Karry/hdd-mp3-player/src/command-v2/font-maly.h

////////////////////////////////////////////////////////////////////////
// Malý fotn 6x8. Protože ale LCD má stránky o výšce 8px a byty 
// se do něj zapisují svisle, tak každé pismeno v tomto fontu je na jednom řádku.

unsigned char rom FontMaly[]={ 
	 0x00, 0x00, 0x00, 0x00, 0x00, 0x00, 	// 0x00 - mezera
	 0x00, 0x00, 0xFE, 0x01, 0x01, 0x01, 	// 0x01 - orámování - levý horní
	 0x00, 0x00, 0xFF, 0x00, 0x00, 0x00, 	// 0x02 - orámování - svislý
	 0x01, 0x01, 0xFE, 0x00, 0x00, 0x00, 	// 0x03 - orámování - pravý horní
	 0x00, 0x00, 0x03, 0x04, 0x04, 0x04, 	// 0x04 - orámování - levý dolní
	 0x04, 0x04, 0x03, 0x00, 0x00, 0x00,	// 0x05 - orámování - pravý dolní	(vodorovné orámování vytvářet nadtržením rádků...)

	 0xFF, 0xC7, 0x83, 0x01, 0x01, 0x01,	// 0x06 - levý konec výběru
	 0x01, 0x01, 0x01, 0x83, 0xC7, 0xFF,	// 0x07 - pravý konce výběru
	 0x7C, 0x00, 0x10, 0x38, 0x7C, 0x00, 	// 0x08 - prehravani - tlac. predchozi
	 0x00, 0x7C, 0x38, 0x10, 0x00, 0x00, 	// 0x09 - prehravani - tlac. play
	 0x00, 0x7C, 0x00, 0x7C, 0x00, 0x00, 	// 0x0A - prehravani - tlac. pause
	 0x00, 0x7C, 0x7C, 0x7C, 0x7C, 0x00, 	// 0x0B - prehravani - tlac. stop
	 0x7C, 0x38, 0x10, 0x00, 0x7C, 0x00, 	// 0x0C - prehravani - tlac. nasledujici
	 0x7C, 0x38, 0x10, 0x7C, 0x38, 0x10,	// 0x0D - prehravani - tlac. previjeni
	 0xC0, 0xFC, 0x04, 0xC8, 0xF8, 0x00, 	// 0x0E - ikonka mp3
	 0x7C, 0x4C, 0x4C, 0x48, 0x78, 0x00, 	// 0x0F - ikonka slozky

	 0xFE, 0xFE, 0xFE, 0xFE, 0xFE, 0xFE, 	// 0x10 - posuvník - 6
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
	0x00, 0x00, 0x00, 0x00, 0x00, 0x00, 	// 0xFB - 
	0x00, 0x00, 0x00, 0x00, 0x00, 0x00, 	// 0xFC - 
	 0x18, 0xA0, 0xA4, 0xA2, 0x78, 0x00,	// 0xFD - ý
	0x00, 0x00, 0x00, 0x00, 0x00, 0x00,  	// 0xFE - 
	0x00, 0x00, 0x00, 0x00, 0x00, 0x00  	// 0xFF - 
};
