Karry/hdd-mp3-player/src/command-v2/font-velky.h

////////////////////////////////////////////////////////////////////////
// Velký fotn 8x16. Protože ale LCD má stránky o výšce 8px a byty 
// se do něj zapisují svisle, tak každé pismeno v tomto fontu je na dvou řádcích.

unsigned char rom FontVelky[]={ 
 0x7C, 0x3A, 0x06, 0x06, 0x06, 0x3A, 0x7C, 0x00,
 0x1F, 0x2E, 0x30, 0x30, 0x30, 0x2E, 0x1F, 0x00,	// 0x00 - digitalni cislice - 0
 0x00, 0x00, 0x00, 0x00, 0x00, 0x3C, 0x7E, 0x00,
 0x00, 0x00, 0x00, 0x00, 0x00, 0x1E, 0x3F, 0x00,	// 0x01 - digitalni cislice - 1
 0x00, 0x82, 0x86, 0x86, 0x86, 0xBA, 0x7C, 0x00,
 0x1F, 0x2E, 0x31, 0x31, 0x31, 0x20, 0x00, 0x00,	// 0x02 - digitalni cislice - 2
 0x00, 0x82, 0x86, 0x86, 0x86, 0xBA, 0x7C, 0x00,
 0x00, 0x20, 0x31, 0x31, 0x31, 0x2E, 0x1F, 0x00,	// 0x03 - digitalni cislice - 3
 0x3E, 0x5C, 0xC0, 0xC0, 0xC0, 0x5C, 0xBE, 0x00,
 0x00, 0x00, 0x00, 0x00, 0x00, 0x0F, 0x1F, 0x00,	// 0x04 - digitalni cislice - 4
 0x7C, 0xBA, 0x86, 0x86, 0x86, 0x82, 0x00, 0x00,
 0x00, 0x20, 0x31, 0x31, 0x31, 0x2E, 0x1F, 0x00,	// 0x05 - digitalni cislice - 5
 0x7C, 0xBA, 0x86, 0x86, 0x86, 0x82, 0x00, 0x00,
 0x1F, 0x2E, 0x31, 0x31, 0x31, 0x2E, 0x1F, 0x00,	// 0x06 - digitalni cislice - 6
 0x00, 0x02, 0x06, 0x06, 0x06, 0x3A, 0x7C, 0x00,
 0x00, 0x00, 0x00, 0x00, 0x00, 0x0E, 0x1F, 0x00,	// 0x07 - digitalni cislice - 7
 0x7C, 0xBA, 0x86, 0x86, 0x86, 0xBA, 0x7C, 0x00,
 0x1F, 0x2E, 0x31, 0x31, 0x31, 0x2E, 0x1F, 0x00,	// 0x08 - digitalni cislice - 8
 0x7C, 0xBA, 0x86, 0x86, 0x86, 0xBA, 0x7C, 0x00,
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
 0x00, 0x80, 0xC7, 0xFE, 0x3F, 0x07, 0x00, 0x00,	//ý
0x00, 0x00, 0x00, 0x00, 0x00, 0x00, 0x00, 0x00,	
0x00, 0x00, 0x00, 0x00, 0x00, 0x00, 0x00, 0x00,		//
0x00, 0x00, 0x00, 0x00, 0x00, 0x00, 0x00, 0x00,	
0x00, 0x00, 0x00, 0x00, 0x00, 0x00, 0x00, 0x00		//
};
