Karry/hdd-mp3-player/src/execution/commands.asm

; XXXXXXXXXXXXXXXXXXXXXXXXXXXXXXXXXXXXXXXXXXXXXXXXXXXXXXXXXXXXXXXXXXXXXXXXXXXXXXXXXXXXXXXXXXXXXXXXXXXXXXXXXXXXXXXXXXXXXXXXXXX
; XXXXXXXXXXXXXXXXXXXXXXXXXXXXXXXXXXXXXXXXXXXXXXXXXXXXXXXXXXXXXXXXXXXXXXXXXXXXXXXXXXXXXXXXXXXXXXXXXXXXXXXXXXXXXXXXXXXXXXXXXXX
; XXXXXXXXXXXXXXXXXXXXXXXXXXXXXXXXXXXXXXXXXXXXXXXXXXXXXXXXXXXXXXXXXXXXXXXXXXXXXXXXXXXXXXXXXXXXXXXXXXXXXXXXXXXXXXXXXXXXXXXXXXX
; tady jsou procedury resici jednotlive prikazy
; Pokud je v zasobniku prikaz pro nejakou proceduru, musi tato procedura nastavit byt STAV_PRIKAZU do 1 (i kdyz treba nema vsechny parametry)
; Pokud procedura najde svuj prikaz a jsou prijate vsechny parametry, musi odeslat nejakou odpoved po USARTu a smazat reg. PRIJATYCH_DAT!!!
; XXXXXXXXXXXXXXXXXXXXXXXXXXXXXXXXXXXXXXXXXXXXXXXXXXXXXXXXXXXXXXXXXXXXXXXXXXXXXXXXXXXXXXXXXXXXXXXXXXXXXXXXXXXXXXXXXXXXXXXXXXX
; CAST 1
CEKEJ_PRIKAZ					; ceka dokud nedostaneme nejaky prikaz
	movfw PRIJATYCH_DAT
	andlw h'FF'
	btfsc STATUS,Z				; koukneme se zda prisel nejaky prikaz...
	goto CEKEJ_PRIKAZ
	return
; XXXXXXXXXXXXXXXXXXXXXXXXXXXXXXXXXXXXXXXXXXXXXXXXXXXXXXXXXXXXXXXXXXXXXXXXXXXXXXXXXXXXXXXXXXXXXXXXXXXXXXXXXXXXXXXXXXXXXXXXXXX
PRIKAZ_02h						; 02h - vrat oddily se systemem FAT32
	movfw 0x078					; prvni byte zasobniku prikazu
	sublw h'02'					
	btfss STATUS,Z
	return						; nebyl prijat prikaz 02h
	bsf STAV_PRIKAZU,0			; mame tu prikaz 02h, nastavime byt STAV_PRIKAZU
	movfw PRIJATYCH_DAT
	sublw .1					; pro prikaz 02h museji prijit 2 byty (prikaz + 1 parametr)
	btfsc STATUS,C
	return						; jeste nemame vsechny parametry
	; Prisel prikaz 02h s jednim parametrem (vrat oddily se systemem FAT32)

	PROG_PAGE_2
	call SCAN_MBR				; najdeme oddily s FAT32 a jejich seznam dame do bufferu 2
	PROG_PAGE_1	
	movfw 0x079					; parametr prikazu 02h (cislo svazku, jehoz parametry chceme vratit)
	andlw b'00000011'			; parametr musi byt v rozsahu 0-3
	movwf TEMP1
	bcf STATUS,C
	rlf TEMP1,F
	rlf TEMP1,F
	rlf TEMP1,F
	rlf TEMP1,W					; parametr vynasobime 16
	addlw 0x10					; buffer 2 je v bance 2 na adrese 0x10
	movwf FSR
	INDF_BANK_2
	movlw .16					; budeme odesilat 16 bytu
	movwf TEMP1
PRIKAZ_02h__ODESILANI_ODDILU
	movfw INDF
	PROG_PAGE_0
	call WR_USART
	PROG_PAGE_1
	incf FSR,F
	decfsz TEMP1,F
	goto PRIKAZ_02h__ODESILANI_ODDILU
	clrf PRIJATYCH_DAT
	return
; XXXXXXXXXXXXXXXXXXXXXXXXXXXXXXXXXXXXXXXXXXXXXXXXXXXXXXXXXXXXXXXXXXXXXXXXXXXXXXXXXXXXXXXXXXXXXXXXXXXXXXXXXXXXXXXXXXXXXXXXXXX
PRIKAZ_04h						; 04h – vrat velikost clusteru
	movfw 0x078					; prvni byte zasobniku prikazu
	sublw h'04'					
	btfss STATUS,Z
	return						; nebyl prijat prikaz 04h
	bsf STAV_PRIKAZU,0			; mame tu prikaz 04h, nastavime byt STAV_PRIKAZU
	; pro prikaz 04h nejsou definovany zadne parametry, proto jiz nic jineho netestujeme

	movfw CLUSTER_SIZE
	PROG_PAGE_0
	call WR_USART
	PROG_PAGE_1
	clrf PRIJATYCH_DAT			; vyprazdnime zasobnik
	return
; XXXXXXXXXXXXXXXXXXXXXXXXXXXXXXXXXXXXXXXXXXXXXXXXXXXXXXXXXXXXXXXXXXXXXXXXXXXXXXXXXXXXXXXXXXXXXXXXXXXXXXXXXXXXXXXXXXXXXXXXXXX
PRIKAZ_05h						; 05h – vrat zaznam v adresari
	movfw 0x078					; prvni byte zasobniku prikazu
	sublw h'05'
	btfss STATUS,Z
	return						; nebyl prijat prikaz 05h
	bsf STAV_PRIKAZU,0			; mame tu prikaz 05h, nastavime byt STAV_PRIKAZU
	movfw PRIJATYCH_DAT
	sublw .6					; pro prikaz 05h musi prijit 7 bytu (prikaz + 6bytu parametr)
	btfsc STATUS,C
	return						; jeste nemame vsechny parametry
	; Prisel prikaz 05h s 6bytovym parametrem 

	movfw 0x079					; nejnizsi cast clusteru adresare
	movwf CLUSTER1
	movfw 0x07A
	movwf CLUSTER2
	movfw 0x07B
	movwf CLUSTER3
	movfw 0x07C
	movwf CLUSTER4
	call PRVNI_CL_ADRESARE

	btfss POZICE,0
	goto PRIKAZ_05h_PAR1_OK

PRIKAZ_05h_PAR1_NOT_OK
	INDF_BANK_2
	movlw 0x10					; 1. byte bufferu 2
	movwf FSR
	movlw h'81'					; jako prvni byte odpovedi dame 81h (Zadany cluster neobsahuje adresar)
	movwf INDF
	goto PRIKAZ_05h_KONEC
PRIKAZ_05h_PAR1_OK

	movfw 0x07D
	movwf ZAZNAM1
	movfw 0x07E
	movwf ZAZNAM2

	call SKOC_NA_ZAZNAM
	btfss POZICE,0
	goto PRIKAZ_05h_PAR2_OK

PRIKAZ_05h_PAR2_NOT_OK
	INDF_BANK_2
	movlw 0x10					; 1. byte bufferu 2
	movwf FSR
	movlw h'80'					; jako prvni byte odpovedi dame 80h (Zadany zaznam mimo rozsah)
	movwf INDF
	goto PRIKAZ_05h_KONEC
PRIKAZ_05h_PAR2_OK

	call FILE_INFO

PRIKAZ_05h_KONEC
	; At uz bylo v zaznamu cokoli, odesleme 16 bytu z BUFFERU 2
	movlw .16
	movwf TEMP1
	PROG_PAGE_0
	call ODESLI_BUFFER2			; odesleme si zaznam o souboru	
	PROG_PAGE_1

	clrf PRIJATYCH_DAT			; vyprazdnime zasobnik prikazu
	return
; XXXXXXXXXXXXXXXXXXXXXXXXXXXXXXXXXXXXXXXXXXXXXXXXXXXXXXXXXXXXXXXXXXXXXXXXXXXXXXXXXXXXXXXXXXXXXXXXXXXXXXXXXXXXXXXXXXXXXXXXXXX
PRIKAZ_06h						; 06h – vrat cislo dalsiho clusteru v alokacnim retezu
	movfw 0x078					; prvni byte zasobniku prikazu
	sublw h'06'					
	btfss STATUS,Z
	return						; nebyl prijat prikaz 06h
	bsf STAV_PRIKAZU,0			; mame tu prikaz 06h, nastavime byt STAV_PRIKAZU
	movfw PRIJATYCH_DAT
	sublw .4					; pro prikaz 06h museji prijit 5 bytu (prikaz + 4byty parametr)
	btfsc STATUS,C
	return						; jeste nemame vsechny parametry
	; Prisel prikaz 06h s 4bytovym parametrem 

	movfw 0x079					; nejnizsi cast clusteru
	movwf CLUSTER1
	movfw 0x07A
	movwf CLUSTER2
	movfw 0x07B
	movwf CLUSTER3
	movfw 0x07C
	movwf CLUSTER4
	PROG_PAGE_0
	call NEXT_CLUSTER
	movfw POZICE				; pokud POZICE = 00h, je vse v poradku (vratime c. dalsiho clusteru v retezci). 
								; Pokud POZICE = FFh byl predany cluster posledni v retezu, nebo byl prazdny...
	call WR_USART
	movfw CLUSTER1
	call WR_USART
	movfw CLUSTER2
	call WR_USART
	movfw CLUSTER3
	call WR_USART
	movfw CLUSTER4
	call WR_USART
	PROG_PAGE_1
	
	clrf PRIJATYCH_DAT			; vyprazdnime zasobnik prikazu
	return
; XXXXXXXXXXXXXXXXXXXXXXXXXXXXXXXXXXXXXXXXXXXXXXXXXXXXXXXXXXXXXXXXXXXXXXXXXXXXXXXXXXXXXXXXXXXXXXXXXXXXXXXXXXXXXXXXXXXXXXXXXXX
PRIKAZ_07h						; 07h – cti cluster
	movfw 0x078					; prvni byte zasobniku prikazu
	sublw h'07'					
	btfss STATUS,Z
	return						; nebyl prijat prikaz 07h
	bsf STAV_PRIKAZU,0			; mame tu prikaz 07h, nastavime byt STAV_PRIKAZU
	movfw PRIJATYCH_DAT
	sublw .4					; pro prikaz 07h museji prijit 5 bytu (prikaz + 4byty parametr)
	btfsc STATUS,C
	return						; jeste nemame vsechny parametry
	; Prisel prikaz 07h s 4bytovym parametrem 

	movfw 0x079					; nejnizsi cast clusteru
	movwf CLUSTER1
	movfw 0x07A
	movwf CLUSTER2
	movfw 0x07B
	movwf CLUSTER3
	movfw 0x07C
	movwf CLUSTER4
	clrf POZICE
	PROG_PAGE_0
	call CLUSTER_TO_LBA			; zjistime si skutecnou polohu pozadovaneho clusteru na disku...
	movfw CLUSTER_SIZE
	movwf SECTOR_C				; tentokrat cteme cely cluster a ne sector
	call READ_SECTOR;S
	PROG_PAGE_1

	movfw CLUSTER_SIZE
	movwf TEMP2					; kolik sektoru budeme odesilat

PRIKAZ_07h__ODESLI_SECTOR
	movlw .0					; budeme odesilat cely sector (256slov = 512bytu)
	movwf TEMP1
	PROG_PAGE_0
	call ODESLI_DATA
	PROG_PAGE_1
	decfsz TEMP2,F 				; a to tolikrat, kolik ma cluster sektroru
	goto PRIKAZ_07h__ODESLI_SECTOR
	
	clrf PRIJATYCH_DAT			; vyprazdnime zasobnik prikazu
	return
; XXXXXXXXXXXXXXXXXXXXXXXXXXXXXXXXXXXXXXXXXXXXXXXXXXXXXXXXXXXXXXXXXXXXXXXXXXXXXXXXXXXXXXXXXXXXXXXXXXXXXXXXXXXXXXXXXXXXXXXXXXX
PRIKAZ_08h						; 08h – zjisti velikost souboru
	movfw 0x078					; prvni byte zasobniku prikazu
	sublw h'08'
	btfss STATUS,Z
	return						; nebyl prijat prikaz 08h
	bsf STAV_PRIKAZU,0			; mame tu prikaz 08h, nastavime byt STAV_PRIKAZU
	movfw PRIJATYCH_DAT
	sublw .6					; pro prikaz 08h musi prijit 7 bytu (prikaz + 6bytu parametr)
	btfsc STATUS,C
	return						; jeste nemame vsechny parametry
	; Prisel prikaz 08h s 6bytovym parametrem 

	movfw 0x079					; nejnizsi cast clusteru adresare
	movwf CLUSTER1
	movfw 0x07A
	movwf CLUSTER2
	movfw 0x07B
	movwf CLUSTER3
	movfw 0x07C
	movwf CLUSTER4
	call PRVNI_CL_ADRESARE

	btfss POZICE,0
	goto PRIKAZ_08h_PAR1_OK

PRIKAZ_08h_PAR1_NOT_OK
	movlw h'81'					; jako prvni byte odpovedi dame 81h (Zadany cluster neobsahuje adresar)
	movwf TEMP1
	goto PRIKAZ_08h_KONEC
PRIKAZ_08h_PAR1_OK

	movfw 0x07D
	movwf ZAZNAM1
	movfw 0x07E
	movwf ZAZNAM2

	call SKOC_NA_ZAZNAM
	btfss POZICE,0
	goto PRIKAZ_08h_PAR2_OK

PRIKAZ_08h_PAR2_NOT_OK
	movlw h'80'					; jako prvni byte odpovedi dame 80h (Zadany zaznam mimo rozsah)
	movwf TEMP1
	goto PRIKAZ_08h_KONEC
PRIKAZ_08h_PAR2_OK

	call FILE_SIZE
	clrf TEMP1

PRIKAZ_08h_KONEC
	; At uz bylo v zaznamu cokoli, odesleme 4 byty z BUFFERU 2
	movfw TEMP1
	PROG_PAGE_0
	call WR_USART
	movlw .4
	movwf TEMP1
	call ODESLI_BUFFER2			; odesleme si zaznam o souboru	
	PROG_PAGE_1

	clrf PRIJATYCH_DAT			; vyprazdnime zasobnik prikazu
	return
; XXXXXXXXXXXXXXXXXXXXXXXXXXXXXXXXXXXXXXXXXXXXXXXXXXXXXXXXXXXXXXXXXXXXXXXXXXXXXXXXXXXXXXXXXXXXXXXXXXXXXXXXXXXXXXXXXXXXXXXXXXX
PRIKAZ_09h						; 09h – hledej zaznam
	movfw 0x078					; prvni byte zasobniku prikazu
	sublw h'09'
	btfss STATUS,Z
	return						; nebyl prijat prikaz 09h
	bsf STAV_PRIKAZU,0			; mame tu prikaz 09h, nastavime byt STAV_PRIKAZU
	movfw PRIJATYCH_DAT
	sublw .7					; pro prikaz 09h musi prijit 8 bytu (prikaz + 7bytu parametr)
	btfsc STATUS,C
	return						; jeste nemame vsechny parametry
	; Prisel prikaz 09h s 5bytovym parametrem 

	movfw 0x079					; nejnizsi cast clusteru adresare
	movwf CLUSTER1
	movfw 0x07A
	movwf CLUSTER2
	movfw 0x07B
	movwf CLUSTER3
	movfw 0x07C
	movwf CLUSTER4
	call PRVNI_CL_ADRESARE

	btfsc POZICE,0
	goto PRIKAZ_09h_SPATNY_PAR

	movfw 0x079					; nejnizsi cast clusteru adresare
	movwf HL_ADR_CL1
	movfw 0x07A
	movwf HL_ADR_CL2
	movfw 0x07B
	movwf HL_ADR_CL3
	movfw 0x07C
	movwf HL_ADR_CL4

	movfw 0x07D
	movwf ZAZNAM1
	movfw 0x07E
	movwf ZAZNAM2

	movfw 0x07F
	movwf HL_PARAMETRY

	call HLEDEJ		; mocna procedura, ktera man podle zadanych parametru vyhleda pozadovany zaznam 
					; a umisti jej do bufferu2 na offset 32 (od zacatku bufferu)
	goto PRIKAZ_09h_KONEC
PRIKAZ_09h_SPATNY_PAR
	BANK_2
	movlw h'81'
	movwf 0x130
	BANK_0
PRIKAZ_09h_KONEC
	movlw .18
	movwf TEMP1	

	PROG_PAGE_0
	call ODESLI_BUFF2_HIGH
	PROG_PAGE_1

	clrf PRIJATYCH_DAT			; vyprazdnime zasobnik prikazu
	return
; XXXXXXXXXXXXXXXXXXXXXXXXXXXXXXXXXXXXXXXXXXXXXXXXXXXXXXXXXXXXXXXXXXXXXXXXXXXXXXXXXXXXXXXXXXXXXXXXXXXXXXXXXXXXXXXXXXXXXXXXXXX
PRIKAZ_0Ah						; 0Ah – precti dlouhe jmeno
	movfw 0x078					; prvni byte zasobniku prikazu
	sublw h'0A'
	btfss STATUS,Z
	return						; nebyl prijat prikaz 0Ah
	bsf STAV_PRIKAZU,0			; mame tu prikaz 0Ah, nastavime byt STAV_PRIKAZU
	movfw PRIJATYCH_DAT
	sublw .6					; pro prikaz 0Ah musi prijit 7 bytu (prikaz + 6bytu parametr)
	btfsc STATUS,C
	return						; jeste nemame vsechny parametry
	; Prisel prikaz 0Ah s 6bytovym parametrem 

	movfw 0x079					; nejnizsi cast clusteru adresare
	movwf HL_ADR_CL1
	movwf CLUSTER1
	movfw 0x07A
	movwf HL_ADR_CL2
	movwf CLUSTER2
	movfw 0x07B
	movwf HL_ADR_CL3
	movwf CLUSTER3
	movfw 0x07C
	movwf HL_ADR_CL4
	movwf CLUSTER4
	call PRVNI_CL_ADRESARE

	btfss POZICE,0
	goto PRIKAZ_0Ah_PAR1_OK

PRIKAZ_0Ah_PAR1_NOT_OK
	INDF_BANK_2
	movlw 0x10					; 1. byte bufferu 2
	movwf FSR
	movlw h'81'					; jako prvni byte odpovedi dame 81h (Zadany cluster neobsahuje adresar)
	movwf POZICE
	goto PRIKAZ_0Ah_KONEC
PRIKAZ_0Ah_PAR1_OK
	movfw 0x07D
	movwf ZAZNAM1
	movfw 0x07E
	movwf ZAZNAM2

	call LONG_NAME
PRIKAZ_0Ah_KONEC
	PROG_PAGE_0
	movfw POZICE
	call WR_USART	
	; At uz bylo v zaznamu cokoli, odesleme 65 bytu z BUFFERU 2
	movlw .65
	movwf TEMP1
	call ODESLI_BUFFER2			; odesleme si zaznam o souboru	
	PROG_PAGE_1

	clrf PRIJATYCH_DAT			; vyprazdnime zasobnik prikazu
	return
; XXXXXXXXXXXXXXXXXXXXXXXXXXXXXXXXXXXXXXXXXXXXXXXXXXXXXXXXXXXXXXXXXXXXXXXXXXXXXXXXXXXXXXXXXXXXXXXXXXXXXXXXXXXXXXXXXXXXXXXXXXX
PRIKAZ_80h						; 80h – hraj mp3 soubor
	movfw 0x078					; prvni byte zasobniku prikazu
	sublw h'80'
	btfss STATUS,Z
	return						; nebyl prijat prikaz 80h
	bsf STAV_PRIKAZU,0			; mame tu prikaz 80h, nastavime byt STAV_PRIKAZU
	movfw PRIJATYCH_DAT
	sublw .6					; pro prikaz 80h musi prijit 7 bytu (prikaz + 6bytu parametr)
	btfsc STATUS,C
	return						; jeste nemame vsechny parametry
	; Prisel prikaz 80h s 6bytovym parametrem 

	movfw 0x079					; nejnizsi cast clusteru adresare
	movwf CLUSTER1
	movfw 0x07A
	movwf CLUSTER2
	movfw 0x07B
	movwf CLUSTER3
	movfw 0x07C
	movwf CLUSTER4
	call PRVNI_CL_ADRESARE

	btfss POZICE,0
	goto PRIKAZ_80h_PAR1_OK

PRIKAZ_80h_PAR1_NOT_OK
	INDF_BANK_2
	movlw 0x10					; 1. byte bufferu 2
	movwf FSR
	movlw h'81'					; jako prvni byte odpovedi dame 81h (Zadany cluster neobsahuje adresar)
	movwf INDF
	goto PRIKAZ_80h_KONEC
PRIKAZ_80h_PAR1_OK

	movfw 0x07D
	movwf ZAZNAM1
	movfw 0x07E
	movwf ZAZNAM2

	call SKOC_NA_ZAZNAM
	btfss POZICE,0
	goto PRIKAZ_80h_PAR2_OK

PRIKAZ_80h_PAR2_NOT_OK
	INDF_BANK_2
	movlw 0x10					; 1. byte bufferu 2
	movwf FSR
	movlw h'80'					; jako prvni byte odpovedi dame 80h (Zadany zaznam mimo rozsah)
	movwf INDF
	goto PRIKAZ_80h_KONEC
PRIKAZ_80h_PAR2_OK

	call FILE_INFO

	INDF_BANK_2
	movlw 0x10					; 1. byte bufferu 2
	movwf FSR
	movfw INDF
	sublw h'06'					; pokud na zadanem miste se nachazi soubor s priponou mp3...
	btfss STATUS,Z
	goto PRIKAZ_80h_KONEC
			
	; ...nastavime jej jako prehravany soubor.
	movlw 0x1C					; 13. byte bufferu 2
	movwf FSR
	movfw INDF
	movwf PREH_DATA_CL1
	movwf CLUSTER1
	incf FSR,f
	movfw INDF
	movwf PREH_DATA_CL2
	movwf CLUSTER2
	incf FSR,f
	movfw INDF
	movwf PREH_DATA_CL3
	movwf CLUSTER3
	incf FSR,f
	movfw INDF
	movwf PREH_DATA_CL4
	movwf CLUSTER4

	PROG_PAGE_0
	call ZJISTI_FRAGMENT
	PROG_PAGE_1
; v CLUSTER[1-4] prijme cislo clusteru a do FRAGMENT[1-2] umisti kolik clusteru 
; po tomto clusteru nasledujich (vcetne) tvori jeden fragment

; Pokud soucasny cluster je prazdny (coz by se stat nemelo) vrati v POZICE FFh
; Jinak, pokud s vse povede, dame do POZICE 0

; ! PODPROGRAM NENI POUZITELNY PRO CLUSTER 0 (prvni cluster ROOT adresare)
; ! PODPROGRAM NETESTUJE ZDA NEBYLO ZADANO VETSI CISLO NEZ JE POCET CLUSTERU !!!
	movfw FRAGMENT1
	movwf PREH_D_FRAGMENT1
	movfw FRAGMENT2
	movwf PREH_D_FRAGMENT2
	
	movfw 0x07D
	movwf PREH_ZAZNAM1
	movfw 0x07E
	movwf PREH_ZAZNAM2

	movfw 0x079					; nejnizsi cast clusteru adresare
	movwf PREH_ADR_CL1
	movfw 0x07A
	movwf PREH_ADR_CL2
	movfw 0x07B
	movwf PREH_ADR_CL3
	movfw 0x07C
	movwf PREH_ADR_CL4
	; aktualni prehravany soubor i prehravana slozka byly nastaveny...

	clrf PREH_DATA_POZICE
	bsf PREH_STAV0,0
	bsf PREH_STAV0,1			; nastavime si vlastosti prehravani: (PREH_STAV[0-1])

	bcf VSREG_MODE_L,1			; prehravame normalni rychlosti 
	bcf PREH_STAV1,0			; prehravame normalni rychlosti 
	
	call VS_SOFT_RESET

	movlw VSADDR_MODE
	movwf TEMP1
	movfw VSREG_MODE_L
	movwf TEMP2
	clrf TEMP3
	call VS_WR_REG

PRIKAZ_80h_KONEC
	; At uz bylo v zaznamu cokoli, odesleme 1 byt z BUFFERU 2
	INDF_BANK_2
	movlw 0x10					; 1. byte bufferu 2
	movwf FSR
	movfw INDF
	PROG_PAGE_0
	call WR_USART	
	PROG_PAGE_1
	
	clrf PRIJATYCH_DAT			; vyprazdnime zasobnik prikazu
	return
; XXXXXXXXXXXXXXXXXXXXXXXXXXXXXXXXXXXXXXXXXXXXXXXXXXXXXXXXXXXXXXXXXXXXXXXXXXXXXXXXXXXXXXXXXXXXXXXXXXXXXXXXXXXXXXXXXXXXXXXXXXX
PRIKAZ_81h						; 81h – vrat stav prehravaneho souboru
	movfw 0x078					; prvni byte zasobniku prikazu
	sublw h'81'
	btfss STATUS,Z
	return						; nebyl prijat prikaz 81h
	bsf STAV_PRIKAZU,0			; mame tu prikaz 81h, nastavime byt STAV_PRIKAZU
	; pro prikaz 81h nejsou definovany zadne parametry, proto jiz nic jineho netestujeme

	movfw PREH_STAV0
	PROG_PAGE_0
	call WR_USART
	PROG_PAGE_1

	movfw PREH_STAV1
	PROG_PAGE_0
	call WR_USART
	PROG_PAGE_1

	bcf PREH_STAV0,2			; 2. bit je nastaven, kdyz se zmeni prehravany soubor (bez volani prikazu) do doby, nez prijde prikaz na dotaz STAVU... (81h)

	movlw VSADDR_DECODE_TIME
	movwf TEMP1
	call VS_RD_REG				; zjistime si aktualni pozici v souboru v sekundach
	movfw TEMP2
	PROG_PAGE_0
	call WR_USART
	movfw TEMP3
	call WR_USART
	PROG_PAGE_1

	clrf PRIJATYCH_DAT			; vyprazdnime zasobnik
	return
; XXXXXXXXXXXXXXXXXXXXXXXXXXXXXXXXXXXXXXXXXXXXXXXXXXXXXXXXXXXXXXXXXXXXXXXXXXXXXXXXXXXXXXXXXXXXXXXXXXXXXXXXXXXXXXXXXXXXXXXXXXX
PRIKAZ_82h						; 82h – nastav hlasitost
	movfw 0x078					; prvni byte zasobniku prikazu
	sublw h'82'
	btfss STATUS,Z
	return						; nebyl prijat prikaz 82h
	bsf STAV_PRIKAZU,0			; mame tu prikaz 82h, nastavime byt STAV_PRIKAZU
	movfw PRIJATYCH_DAT
	sublw .2					; pro prikaz 82h museji prijit 3 byty (prikaz + 2byty parametr)
	btfsc STATUS,C
	return						; jeste nemame vsechny parametry
	; Prisel prikaz 82h s 2bytovym parametrem 

	movfw 0x079					; hlasitost pro levy kanal
	movwf VSREG_VOL_H
	movfw 0x07A					; hlasitost pro pravy kanal
	movwf VSREG_VOL_L
	call VS_SET_VOLUME			; nastavime hlasitost	

	movlw h'FF'
	PROG_PAGE_0
	call WR_USART
	PROG_PAGE_1
	clrf PRIJATYCH_DAT			; vyprazdnime zasobnik
	return
; XXXXXXXXXXXXXXXXXXXXXXXXXXXXXXXXXXXXXXXXXXXXXXXXXXXXXXXXXXXXXXXXXXXXXXXXXXXXXXXXXXXXXXXXXXXXXXXXXXXXXXXXXXXXXXXXXXXXXXXXXXX
PRIKAZ_83h						; 83h – vrat informace o prehravanem souboru
	movfw 0x078					; prvni byte zasobniku prikazu
	sublw h'83'
	btfss STATUS,Z
	return						; nebyl prijat prikaz 83h
	bsf STAV_PRIKAZU,0			; mame tu prikaz 83h, nastavime byt STAV_PRIKAZU
	; pro prikaz 83h nejsou definovane zadne parametry, proto jiz nic jineho netestujeme

	movlw VSADDR_AUDATA
	movwf TEMP1
	call VS_RD_REG
	movfw TEMP2
	PROG_PAGE_0
	call WR_USART
	movfw TEMP3
	call WR_USART	
	PROG_PAGE_1
	; odeslali jsme AUDATA

	movlw VSADDR_HDAT0
	movwf TEMP1
	call VS_RD_REG
	movfw TEMP2
	PROG_PAGE_0
	call WR_USART
	movfw TEMP3
	call WR_USART	
	PROG_PAGE_1
	; odeslali jsme HDAT0

	movlw VSADDR_HDAT1
	movwf TEMP1
	call VS_RD_REG
	movfw TEMP2
	PROG_PAGE_0
	call WR_USART
	movfw TEMP3
	call WR_USART	
	; odeslali jsme HDAT1

	movfw PREH_ADR_CL1
	call WR_USART
	movfw PREH_ADR_CL2
	call WR_USART
	movfw PREH_ADR_CL3
	call WR_USART
	movfw PREH_ADR_CL4
	call WR_USART

	movfw PREH_ZAZNAM1
	call WR_USART
	movfw PREH_ZAZNAM2
	call WR_USART
	PROG_PAGE_1

	clrf PRIJATYCH_DAT			; vyprazdnime zasobnik
	return
; XXXXXXXXXXXXXXXXXXXXXXXXXXXXXXXXXXXXXXXXXXXXXXXXXXXXXXXXXXXXXXXXXXXXXXXXXXXXXXXXXXXXXXXXXXXXXXXXXXXXXXXXXXXXXXXXXXXXXXXXXXX
PRIKAZ_84h						; 84h – nastav stav prehravani
	movfw 0x078					; prvni byte zasobniku prikazu
	sublw h'84'
	btfss STATUS,Z
	return						; nebyl prijat prikaz 84h
	bsf STAV_PRIKAZU,0			; mame tu prikaz 84h, nastavime byt STAV_PRIKAZU
	movfw PRIJATYCH_DAT
	sublw .2					; pro prikaz 8h museji prijit 3 byty (prikaz + 2byty parametr)
	btfsc STATUS,C
	return						; jeste nemame vsechny parametry
	; Prisel prikaz 84h s 2bytovym parametrem 

	movfw PREH_STAV0
	andlw b'00000110'
	movwf PREH_STAV0
	movfw 0x079					; parametr 1
	andlw b'11111001'			; nektere bity vymaskujeme (vsechny nelze ovladat prikazem)
	iorwf PREH_STAV0,w	
	movwf PREH_STAV0

	movfw 0x07A					; parametr 2
	movwf PREH_STAV1

	bcf VSREG_MODE_L,1			; prehravame normalni rychlosti (zda se mp3 prevyji je reseno v hlavni smycce podle stavu registru PREH_STAV1)
	bcf VSREG_MODE_L,7			;bass/treble enhancer
	btfsc PREH_STAV1,3			; 3. bit =	1 => zvyrazneni basu a vysek (moznost dekoderu vs1001 "bass/treble enhancer")
	bsf VSREG_MODE_L,7			;bass/treble enhancer
	
	movlw VSADDR_MODE
	movwf TEMP1
	movfw VSREG_MODE_L
	movwf TEMP2
	clrf TEMP3
	call VS_WR_REG
	
	movlw VSADDR_STATUS
	call VS_RD_REG
	movfw TEMP2
	movwf VSREG_STATUS_L

	bcf VSREG_STATUS_L,2		; Bit 2 is analog powerdown bit.
	btfsc PREH_STAV1,4			; 4. bit = 1 => MUTE
	bsf VSREG_STATUS_L,2		; Bit 2 is analog powerdown bit.
	
	movlw VSADDR_STATUS
	movwf TEMP1
	movfw VSREG_STATUS_L
	movwf TEMP2
	clrf TEMP3
	call VS_WR_REG

	btfss PREH_STAV1,4			; 4. bit = 1 => MUTE
	call VS_SET_VOLUME			; nastavime hlasitost
								; nevim sice proc, ale kdyz prepisu VS reg. STATUS, zmeni se hlasitost

	PROG_PAGE_0
	movlw h'FF'
	call WR_USART
	PROG_PAGE_1
	clrf PREH_CITAC_PREV
	clrf PRIJATYCH_DAT			; vyprazdnime zasobnik
	return
; XXXXXXXXXXXXXXXXXXXXXXXXXXXXXXXXXXXXXXXXXXXXXXXXXXXXXXXXXXXXXXXXXXXXXXXXXXXXXXXXXXXXXXXXXXXXXXXXXXXXXXXXXXXXXXXXXXXXXXXXXXX
