Karry/hdd-mp3-player/src/execution/vs1001.asm

;**********************************************************
;**********************************************************
;**********************************************************
; OBSLUZNE PODPROGRAMY PRO MP3 DECODER vs1001g
;**********************************************************
;**********************************************************
;**********************************************************

; MP3_PORT		
; MP3_PORT_TRIS	

; BITY MP3_PORT
; #define MP3_SO		MP3_PORT,0	; serial output - tady dostavame z dekoderu data
; #define MP3_SI		MP3_PORT,1	; serial input  - pokud MP3_CS=1, tak posilame mp3 data, pokud =0, tak posilame prikaz
; #define MP3_SCLK		MP3_PORT,2	; clock - nabezna hrana urcuje platnost dat pri seriovem prenosu
; #define MP3_CS		MP3_PORT,3	; cable select  - pokud MP3_CS=1, tak po SI posilame mp3 data, pokud =0, tak posilame prikaz
; #define MP3_DREQ		MP3_PORT,4	; data request  - pokud =1, tak dekoder pozaduje dalsi mp3 data (vic jak 32B)
; #define MP3_BSYNC		MP3_PORT,5	; pro synchronizaci - ma byt nastaven pri prvnim prenasenem bitu kazdeho bytu

;**********************************************************
; co nejrychleji vodesle hodnotu ve W smerem k dekoderu (obsluhuje signaly DSYNC, SI, SCLK)
VS_WR_BYTE
#IF SPI_SOFTWARE==1
	bsf MP3_BSYNC		; bude nasledovat prvni bit bytu, proto nastavime BSYNC
	movwf SSPBUF		; dame dato do SPI bufferu
	nop
	nop
	nop
	nop
	nop
	nop
	bcf MP3_BSYNC
	btfss PIR1,SSPIF	; 3. bit
	goto $-1			; cekame dokud neni prenos kompletni
	bcf PIR1,SSPIF		; 
	return
#ELSE
	; k praci pouziva TEMPW
	movwf TEMPW		; dato co mame odeslat si hodime do tempu...

	bsf MP3_BSYNC	; bude nasledovat prvni bit bytu, proto nastavime BSYNC

	; 7. bit bytu
	bcf MP3_SCLK	; shodime SCLK
	bcf MP3_SI		; nevime zda bit bude 0 nebo 1, SI nulujeme
	rlf TEMPW,f		; odesilame od nejvyssiho bitu k nejnizsimu
	btfsc STATUS,C
	bsf MP3_SI
	bsf MP3_SCLK
	bcf MP3_BSYNC
	
	; 6. bit bytu
	bcf MP3_SCLK	; shodime SCLK
	bcf MP3_SI		; nevime zda bit bude 0 nebo 1, SI nulujeme
	rlf TEMPW,f		; odesilame od nejvyssiho bitu k nejnizsimu
	btfsc STATUS,C
	bsf MP3_SI
	bsf MP3_SCLK

	; 5. bit bytu
	bcf MP3_SCLK	; shodime SCLK
	bcf MP3_SI		; nevime zda bit bude 0 nebo 1, SI nulujeme
	rlf TEMPW,f		; odesilame od nejvyssiho bitu k nejnizsimu
	btfsc STATUS,C
	bsf MP3_SI
	bsf MP3_SCLK

	; 4. bit bytu
	bcf MP3_SCLK	; shodime SCLK
	bcf MP3_SI		; nevime zda bit bude 0 nebo 1, SI nulujeme
	rlf TEMPW,f		; odesilame od nejvyssiho bitu k nejnizsimu
	btfsc STATUS,C
	bsf MP3_SI
	bsf MP3_SCLK

	; 3. bit bytu
	bcf MP3_SCLK	; shodime SCLK
	bcf MP3_SI		; nevime zda bit bude 0 nebo 1, SI nulujeme
	rlf TEMPW,f		; odesilame od nejvyssiho bitu k nejnizsimu
	btfsc STATUS,C
	bsf MP3_SI
	bsf MP3_SCLK

	; 2. bit bytu
	bcf MP3_SCLK	; shodime SCLK
	bcf MP3_SI		; nevime zda bit bude 0 nebo 1, SI nulujeme
	rlf TEMPW,f		; odesilame od nejvyssiho bitu k nejnizsimu
	btfsc STATUS,C
	bsf MP3_SI
	bsf MP3_SCLK

	; 1. bit bytu
	bcf MP3_SCLK	; shodime SCLK
	bcf MP3_SI		; nevime zda bit bude 0 nebo 1, SI nulujeme
	rlf TEMPW,f		; odesilame od nejvyssiho bitu k nejnizsimu
	btfsc STATUS,C
	bsf MP3_SI
	bsf MP3_SCLK

	; 0. bit bytu
	bcf MP3_SCLK	; shodime SCLK
	bcf MP3_SI		; nevime zda bit bude 0 nebo 1, SI nulujeme
	rlf TEMPW,f		; odesilame od nejvyssiho bitu k nejnizsimu
	btfsc STATUS,C
	bsf MP3_SI
	bsf MP3_SCLK

	bcf MP3_SCLK
	return
#ENDIF
;**********************************************************
; co nejrychleji prijme dato z vs1001 a umisti jej do W
VS_RD_BYTE
#IF SPI_SOFTWARE==1
	bsf MP3_BSYNC		; bude nasledovat prvni bit bytu, proto nastavime BSYNC
	movlw .0
	movwf SSPBUF		; dame dato do SPI bufferu
	nop
	nop
	nop
	nop
	nop
	nop
	bcf MP3_BSYNC
	btfss PIR1,SSPIF
	goto $-1			; cekame dokud neni prenos kompletni
	bcf PIR1,SSPIF
	movfw SSPBUF
	return
#ELSE
	; k praci pouziva TEMPW

	clrf TEMPW		; vymazeme, sem budeme strkat dato co nam prijde...
	bcf MP3_SCLK	; shodime SCLK
	bsf MP3_BSYNC	; bude nasledovat prvni bit bytu, proto nastavime BSYNC
	bcf STATUS,C	; nulujeme priznak CARRY, staci to delat jen na zacatku, protoze TEMW mame prazdny...

	; 7. bit bytu
	bsf MP3_SCLK	; nabezna hrana SCLK
	btfsc MP3_SO
	bsf STATUS,C	; pokud je SO v jednice nastavime C...
	rlf TEMPW,f
	bcf MP3_SCLK	; shodime SCLK

	bcf MP3_BSYNC

	; 6. bit bytu
	bsf MP3_SCLK	; nabezna hrana SCLK
	btfsc MP3_SO
	bsf STATUS,C	; pokud je SO v jednice nastavime C...
	rlf TEMPW,f
	bcf MP3_SCLK	; shodime SCLK	

	; 5. bit bytu
	bsf MP3_SCLK	; nabezna hrana SCLK
	btfsc MP3_SO
	bsf STATUS,C	; pokud je SO v jednice nastavime C...
	rlf TEMPW,f
	bcf MP3_SCLK	; shodime SCLK	

	; 4. bit bytu
	bsf MP3_SCLK	; nabezna hrana SCLK
	btfsc MP3_SO
	bsf STATUS,C	; pokud je SO v jednice nastavime C...
	rlf TEMPW,f
	bcf MP3_SCLK	; shodime SCLK	

	; 3. bit bytu
	bsf MP3_SCLK	; nabezna hrana SCLK
	btfsc MP3_SO
	bsf STATUS,C	; pokud je SO v jednice nastavime C...
	rlf TEMPW,f
	bcf MP3_SCLK	; shodime SCLK	

	; 2. bit bytu
	bsf MP3_SCLK	; nabezna hrana SCLK
	btfsc MP3_SO
	bsf STATUS,C	; pokud je SO v jednice nastavime C...
	rlf TEMPW,f
	bcf MP3_SCLK	; shodime SCLK	

	; 1. bit bytu
	bsf MP3_SCLK	; nabezna hrana SCLK
	btfsc MP3_SO
	bsf STATUS,C	; pokud je SO v jednice nastavime C...
	rlf TEMPW,f
	bcf MP3_SCLK	; shodime SCLK	

	; 0. bit bytu
	bsf MP3_SCLK	; nabezna hrana SCLK
	btfsc MP3_SO
	bsf STATUS,C	; pokud je SO v jednice nastavime C...
	rlf TEMPW,W
	bcf MP3_SCLK	; shodime SCLK	

	; movfw TEMPW ; tuto operaci jiz nemusime provadet, protoze jsme posledni rotaci hodily do W (rlf TEMPW,W)
	return
#ENDIF
;**********************************************************
; do TEMP1 dame adresu registru 
; do TEMP2 dame dolni slabiku zapisovaneho slova
; do TEMP3 dame horni slabiku zapisovaneho slova
VS_WR_REG	; zapise 16bitove slovo (TEMP2,TEMP3) do registru mp3 dekoderu (TEMP1)
			; 16bit dato se odesila od nejvyssiho bitu (15,14...8,7...1,0)
			; kde TEMP3 = bity 15-8 ; TEMP2 = bity 7-0
; pri praci pouziva TEMP1, TEMP2, TEMP3, TEMPW
	btfss MP3_DREQ
	goto $-1
	; v datasheetu k VS1001k o tom sice nic nepisou, v diskuzi na ikoras.iglu.cz mi bylo al porazeno, 
	; ze necekani na DREQ pri cteni/zapisu registru muze zpusobovat praskani n vystupu...

	bcf MP3_CS			; po SI posilame prikaz
	movlw b'00000010'	; write
	call VS_WR_BYTE	
	movfw TEMP1			; adresa zapisovaneho registru
	call VS_WR_BYTE
	movfw TEMP3 		; horni slabika
	call VS_WR_BYTE
	movfw TEMP2 		; dolni slabika
	call VS_WR_BYTE

	call DELAY_5us		; pozor, prepise TEMP1
	bsf MP3_CS
	return
;**********************************************************
; do TEMP1 dame adresu registru 
; v TEMP2 nam vrati dolni slabiku precteneho slova
; v TEMP3 nam vrati horni slabiku precteneho slova
VS_RD_REG	; precte 16bitove slovo (TEMP3,TEMP2) z registru mp3 dekoderu (TEMP1)
			; kde TEMP3 = bity 15-8 ; TEMP2 = bity 7-0
; pri praci pouziva TEMP1, TEMP2, TEMP3, TEMPW
	btfss MP3_DREQ
	goto $-1
	; v datasheetu k VS1001k o tom sice nic nepisou, v diskuzi na ikoras.iglu.cz mi bylo al porazeno, 
	; ze necekani na DREQ pri cteni/zapisu registru muze zpusobovat praskani n vystupu...

	bcf MP3_CS			; po SI posilame prikaz
	movlw b'00000011'	; read
	call VS_WR_BYTE	
	movfw TEMP1			; adresa cteneho registru
	call VS_WR_BYTE
	call VS_RD_BYTE
	movwf TEMP3 		; horni slabika
	call VS_RD_BYTE
	movwf TEMP2 		; dolni slabika

	call DELAY_5us		; pozor, prepise TEMP1
	bsf MP3_CS
	return
;**********************************************************
VS_SOFT_RESET_NO_PLUG	; provede softwarovy reset dekoderu bez resetu pluginu
	PROG_PAGE_0
	call DELAY_200ms
	PROG_PAGE_1

	movlw VSADDR_MODE
	movwf TEMP1
	bsf VSREG_MODE_L,2	; soft reset=1
	movfw VSREG_MODE_L
	movwf TEMP2
	movlw .0			; MODE_H
	movwf TEMP3
	call VS_WR_REG

	PROG_PAGE_0
	call DELAY_2ms
	PROG_PAGE_1
	call VS_SEND_1024_NULL	

	bcf VSREG_MODE_L,2	; soft reset=0
	return
;**********************************************************
VS_SOFT_RESET	; provede softwarovy reset dekoderu (pri zapnuti a pote po skonceni kazde mp3)
	PROG_PAGE_0
	call DELAY_200ms
	PROG_PAGE_1

	movlw VSADDR_MODE
	movwf TEMP1
	bsf VSREG_MODE_L,2	; soft reset=1
	movfw VSREG_MODE_L
	movwf TEMP2
	movlw .0			; MODE_H
	movwf TEMP3
	call VS_WR_REG

	PROG_PAGE_0
	call DELAY_2ms
	PROG_PAGE_1
	call VS_SEND_1024_NULL	

	bcf VSREG_MODE_L,2	; soft reset=0

	movlw VSADDR_AIADDR
	movwf TEMP1
	movlw 0x00
	movwf TEMP2	
	movlw 0x42
	movwf TEMP3
	call VS_WR_REG				; nastavime zacatek uzivatelskeho programu (0x4200)

	movlw VSADDR_AICTRL0
	movwf TEMP1
	movlw 0x00
	movwf TEMP2	
	movlw 0x00
	movwf TEMP3
	call VS_WR_REG				; resetujeme plugin

	movlw VSADDR_AICTRL0
	movwf TEMP1
	movlw VS_LOUDNESS
	movwf TEMP2	
	movlw 0x00
	movwf TEMP3
	call VS_WR_REG				; nastavime pouzivany filter

	movfw VS_LOUDNESS
	andlw h'FF'
	btfss STATUS,Z
	return

	movlw VSADDR_AIADDR
	movwf TEMP1
	clrf TEMP2	
	clrf TEMP3
	call VS_WR_REG				; pokud je filter 0, vypneme plugin
	return
;**********************************************************
VS_SEND_32_NULL
	call WAIT_FOR_VSDREQ
	movlw .32
	movwf TEMP2
	
	movlw .0
	call VS_WR_BYTE
	decfsz TEMP2,F
	goto $-3
	return
;**********************************************************
VS_SEND_1024_NULL
	bsf MP3_CS			; po SI posilam data
	movlw .32
	movwf TEMP1

	call VS_SEND_32_NULL
	decfsz TEMP1,F
	goto $-2
	 
	return
;**********************************************************
VS_SET_VOLUME
	movlw VSADDR_VOL
	movwf TEMP1

	movfw VSREG_VOL_L
	movwf TEMP2
	movfw VSREG_VOL_H
	movwf TEMP3
	call VS_WR_REG
	return		
;**********************************************************
WAIT_FOR_VSDREQ
	btfss MP3_DREQ
	goto WAIT_FOR_VSDREQ
	return
;**********************************************************
VS_END_BEEP
	call WAIT_FOR_VSDREQ

	movlw h'45'
	call VS_WR_BYTE
	movlw h'78'
	call VS_WR_BYTE
	movlw h'69'
	call VS_WR_BYTE
	movlw h'74'			; odeslanim tohoto kodu sinusovku ukoncime...
	call VS_WR_BYTE
	movlw .0
	call VS_WR_BYTE
	movlw .0
	call VS_WR_BYTE
	movlw .0
	call VS_WR_BYTE
	movlw .0
	call VS_WR_BYTE

	return
;**********************************************************
VS_BEEP
;	call VS_SOFT_RESET
;	call WAIT_FOR_VSDREQ

	bsf MP3_CS			; po SI posilam data
	movlw h'53'
	call VS_WR_BYTE
	movlw h'EF'
	call VS_WR_BYTE
	movlw h'6E'
	call VS_WR_BYTE
	movlw .62			; ctyr bytova testovaci sekvence. Tento posledni byte znamena, 
	call VS_WR_BYTE		; ze s pouzitim vzorkovaci frekvence 16kHz bude generovan ton 1kHz
	movlw .0
	call VS_WR_BYTE
	movlw .0
	call VS_WR_BYTE
	movlw .0
	call VS_WR_BYTE
	movlw .0			; testovaci kod musi byt nasledovan 4 nulamy
	call VS_WR_BYTE

	return
;**********************************************************
VS_INIT
	clrf VSREG_MODE_L
	clrf VSREG_STATUS_L

	movlw .3
	movwf TEMP5
	call VS_SOFT_RESET_NO_PLUG		; resetujeme
	call VS_SET_VOLUME				; nastavime hlasitost
	decfsz TEMP5,f
	goto $-3
	; pro jistotu jej resetuji 5x za sebou...
	
	movlw .3
	movwf TEMP5
VS_INIT_BEEP
	call VS_BEEP
	PROG_PAGE_0
	call DELAY_200ms
	PROG_PAGE_1
	call VS_END_BEEP
	PROG_PAGE_0
	call DELAY_200ms
	PROG_PAGE_1
	decfsz TEMP5,f
	goto VS_INIT_BEEP
	; pri initu 3x za sebou pipneme (asi pro to ze neposimal uvodni nuly, tak v praxi pipne jenom 2x :)

	call VS_SOFT_RESET_NO_PLUG		; resetujeme

	return
;**********************************************************
DELAY_5us
	; pouziva TEMP1
	; (Fosc = 20 MHz , instr. cyklus= 0.20 us) 5us / 0.20 us = 25 instrukcnich cyklu
	; (Fosc = 16 MHz , instr. cyklus= 0.25 us) 5us / 0.25 us = 20 instrukcnich cyklu
;Variable: TMP0
;Delay 25 cycles
        MOVLW 0x08  ;8 DEC
        MOVWF TEMP1
        DECFSZ TEMP1,F
        GOTO $-1
;End of Delay
	return
;**********************************************************
