Karry/hdd-mp3-player/src/execution/aritmetic.asm

;**********************************************************
;**********************************************************
;**********************************************************
; Obsahuje podrogramy realizujici zakladni aritmeticke operace
; pouzivane v mp3 preprcavaci. Vsechny operace se provadi 
; s 32bitovymi cisly.
; 
; Pro praci aritmetickych procedur je rezervovana BANKA 1 !!!!!
;**********************************************************
;**********************************************************
;**********************************************************
SOUCET
; provede soucet hodnoty v registrech OPERAND_X[1..4] 
; s hodnotou v OPERAND_Y[1..4] a umisti do VYSLEDEK[1..4] 
; pokud dojde k preteceni, nastavi se PRETECENI do 1
; (byty s indexem 1 maji nejnizsi vahu)
	BANK_1
	clrf PRETECENI

	movfw OPERAND_X1
	addwf OPERAND_Y1,W
	movwf VYSLEDEK1
	btfsc STATUS,C
		bsf PRETECENI,1

	movfw OPERAND_X2
	addwf OPERAND_Y2,W
	movwf VYSLEDEK2
	movlw .1
	btfsc STATUS,C
		bsf PRETECENI,0
	btfsc PRETECENI,1
		addwf VYSLEDEK2,F
	btfsc STATUS,C
		bsf PRETECENI,0
	bcf PRETECENI,1

	movfw OPERAND_X3
	addwf OPERAND_Y3,W
	movwf VYSLEDEK3
	movlw .1
	btfsc STATUS,C
		bsf PRETECENI,1
	btfsc PRETECENI,0
		addwf VYSLEDEK3,F
	btfsc STATUS,C
		bsf PRETECENI,1
	bcf PRETECENI,0

	movfw OPERAND_X4
	addwf OPERAND_Y4,W
	movwf VYSLEDEK4
	movlw .1
	btfsc STATUS,C
		bsf PRETECENI,0
	btfsc PRETECENI,1
		addwf VYSLEDEK4,F
	btfsc STATUS,C
		bsf PRETECENI,0
	bcf PRETECENI,1	

	BANK_0
	return
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
		; obsah X zustane nezmenen
	BANK_1
	clrf PRETECENI
	movlw h'FF'	

	andwf OPERAND_X1,F
	btfss STATUS,Z
		bsf PRETECENI,0
	andwf OPERAND_X2,F
	btfss STATUS,Z
		bsf PRETECENI,0
	andwf OPERAND_X3,F
	btfss STATUS,Z
		bsf PRETECENI,0
	andwf OPERAND_X4,F
	btfss STATUS,Z
		bsf PRETECENI,0		

	BANK_0
	return
;**********************************************************
